Alzymologist/Kampela/docs/photos_C/IMG_20230130_222610.jpg

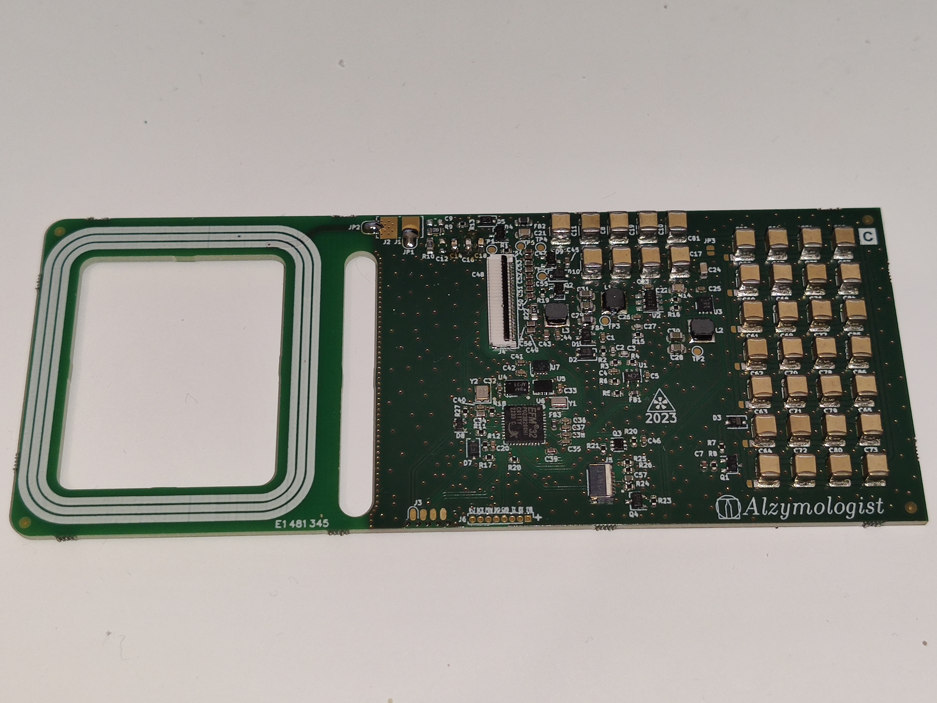
docs/photos_C/IMG_20230130_222610.jpg
