Alzymologist/Kampela/docs/photos_C/IMG_20230130_222933.jpg

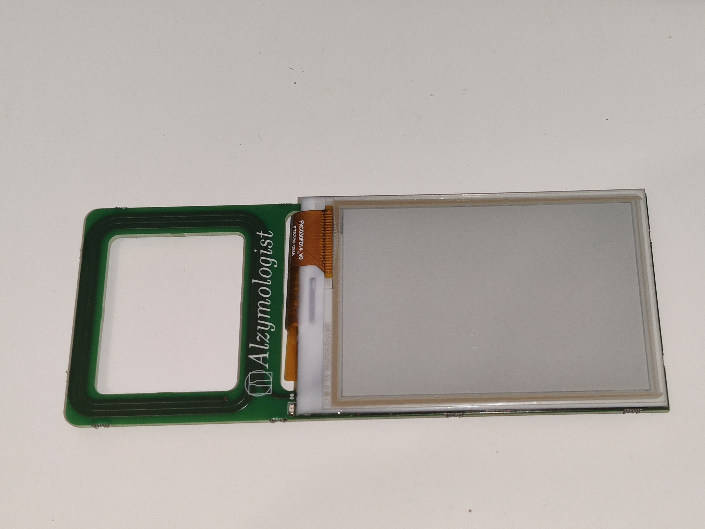
docs/photos_C/IMG_20230130_222933.jpg
