Alzymologist/Kampela/docs/photos_C/IMG_20230130_222946.jpg

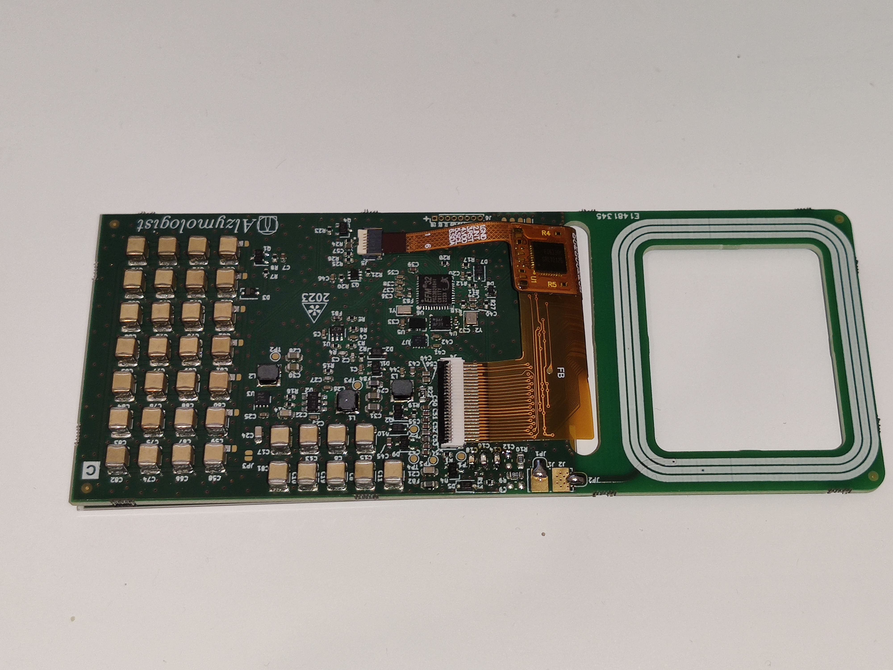
docs/photos_C/IMG_20230130_222946.jpg
