Alzymologist/Kampela/docs/photos_D/frame_1.jpg

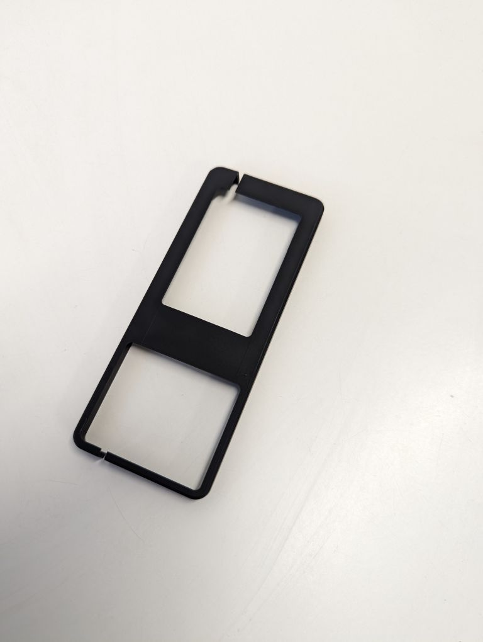
docs/photos_D/frame_1.jpg
