Alzymologist/Kampela/docs/photos_D/frame_2.jpg

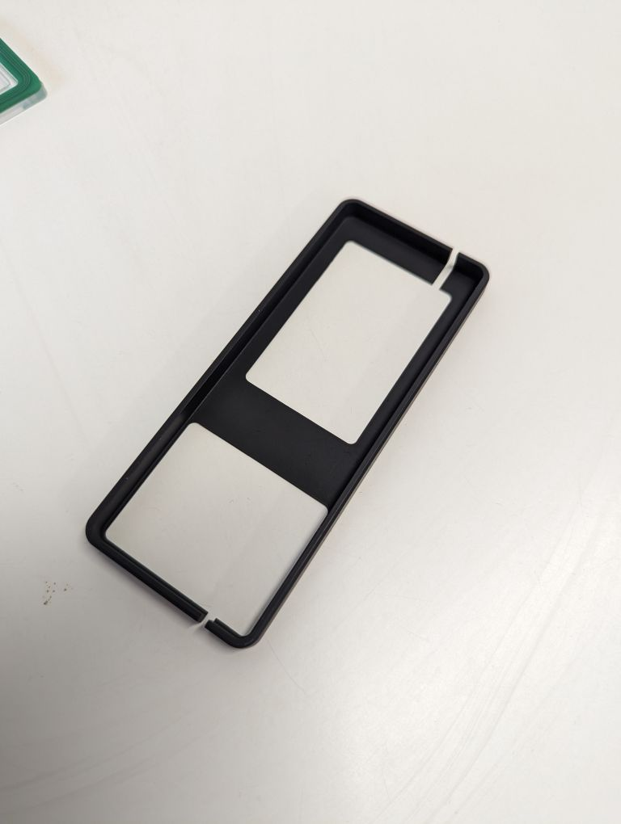
docs/photos_D/frame_2.jpg
