Alzymologist/Kampela/docs/photos_D/frame_3.jpg

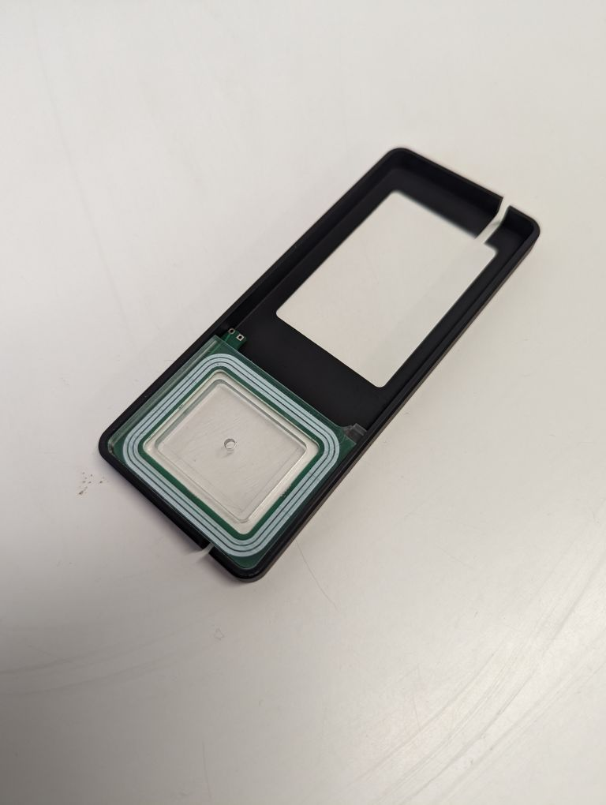
docs/photos_D/frame_3.jpg
