Alzymologist/Kampela/docs/photos_D/frame_4.jpg

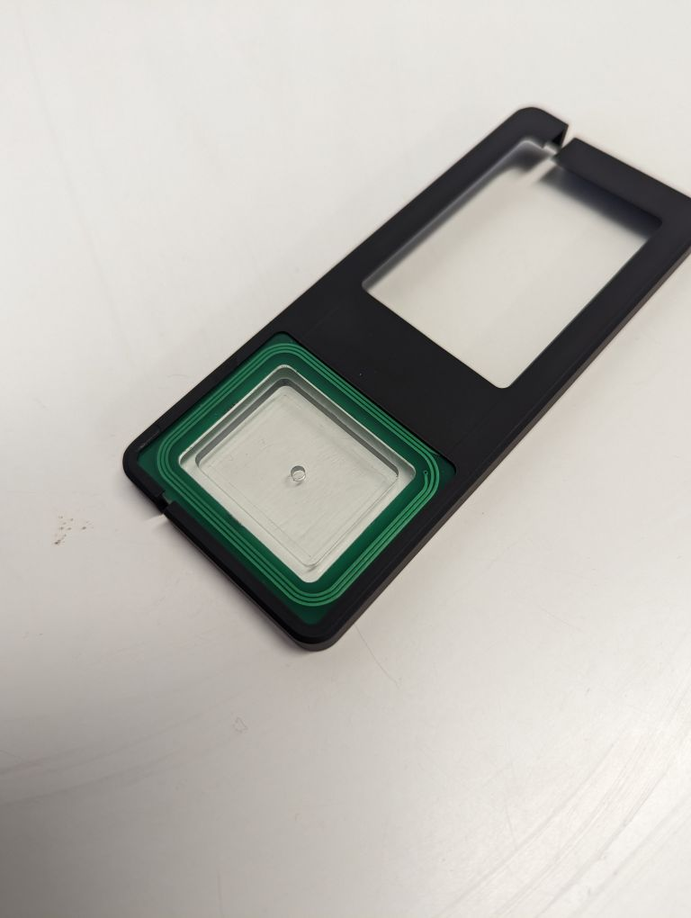
docs/photos_D/frame_4.jpg
