Alzymologist/Kampela/docs/photos_D/frame_5.jpg

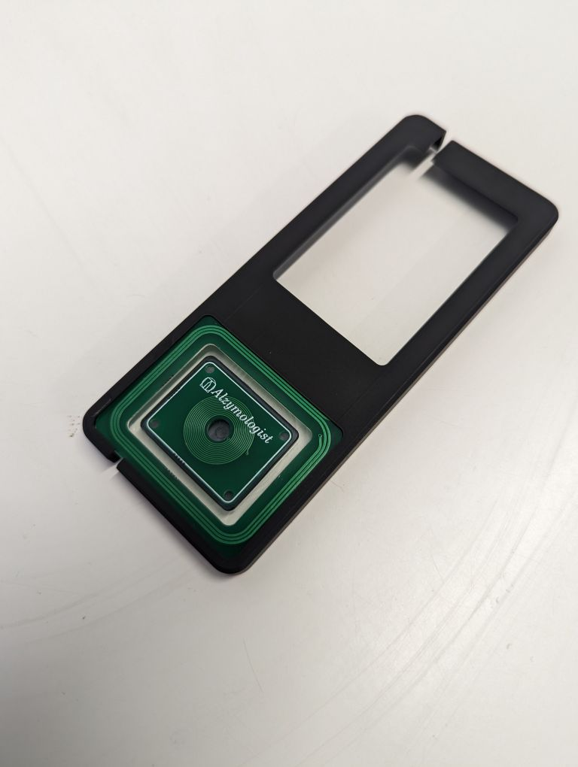
docs/photos_D/frame_5.jpg
