Alzymologist/Kampela/docs/photos_D/PCB_1.jpg

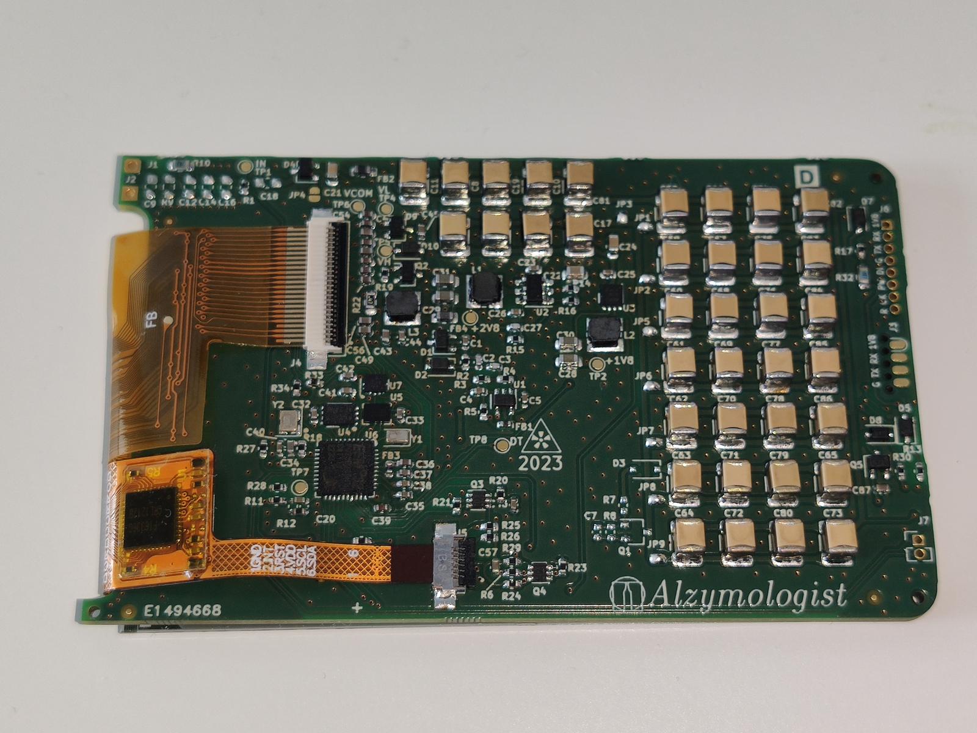
docs/photos_D/PCB_1.jpg
