Alzymologist/Kampela/docs/photos_D/PCB_2.jpg

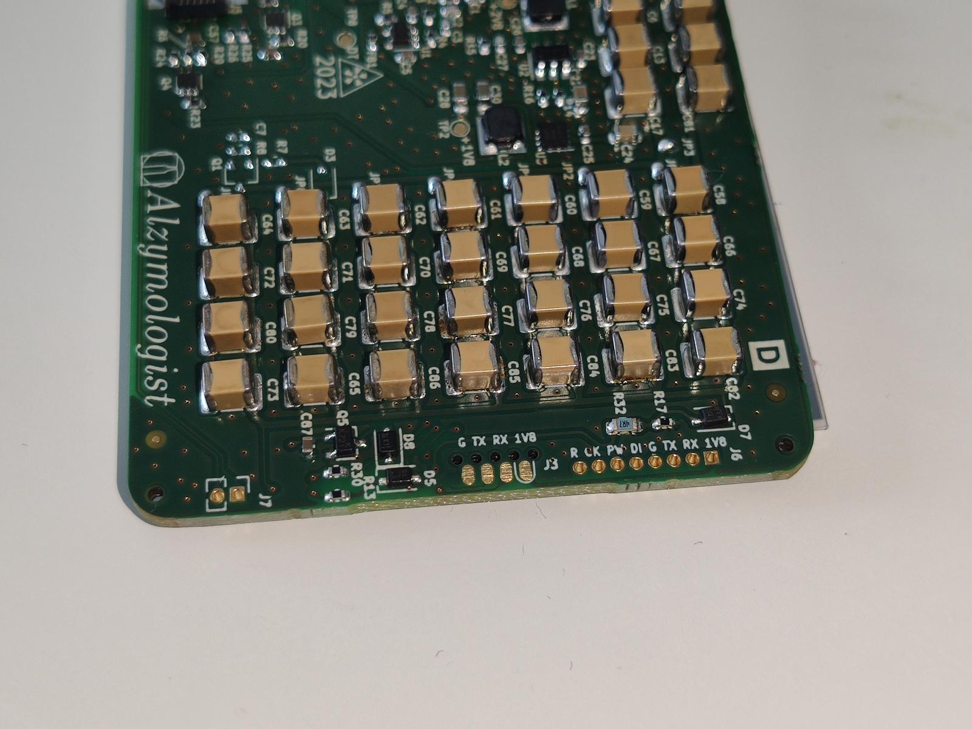
docs/photos_D/PCB_2.jpg
