Alzymologist/Kampela/docs/photos_D/PCB_3.jpg

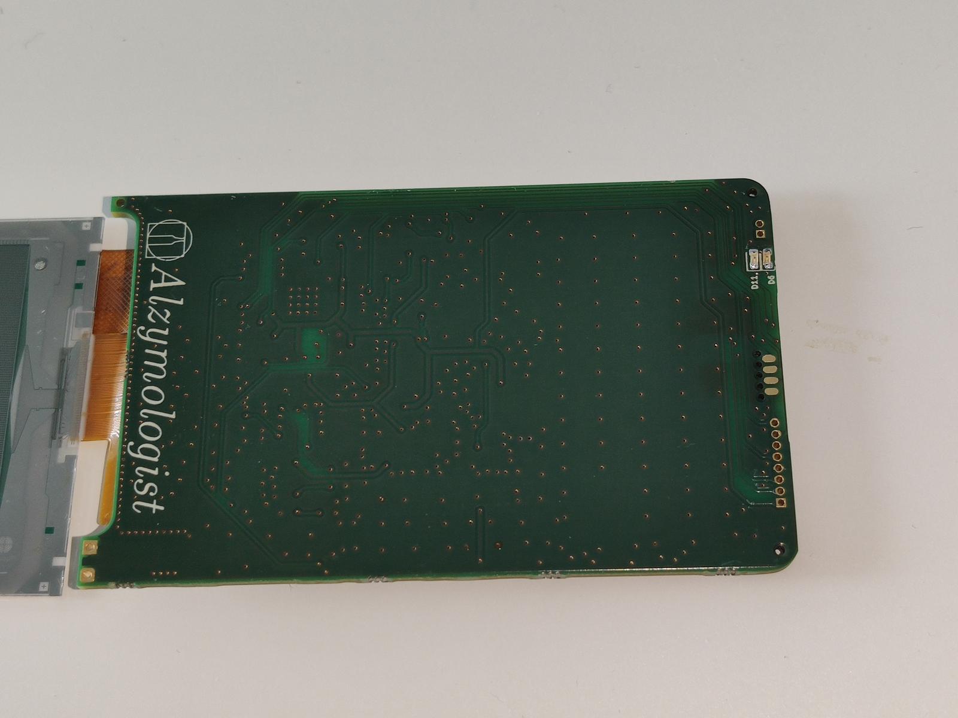
docs/photos_D/PCB_3.jpg
