Alzymologist/Kampela/docs/photos_D/tag.jpg

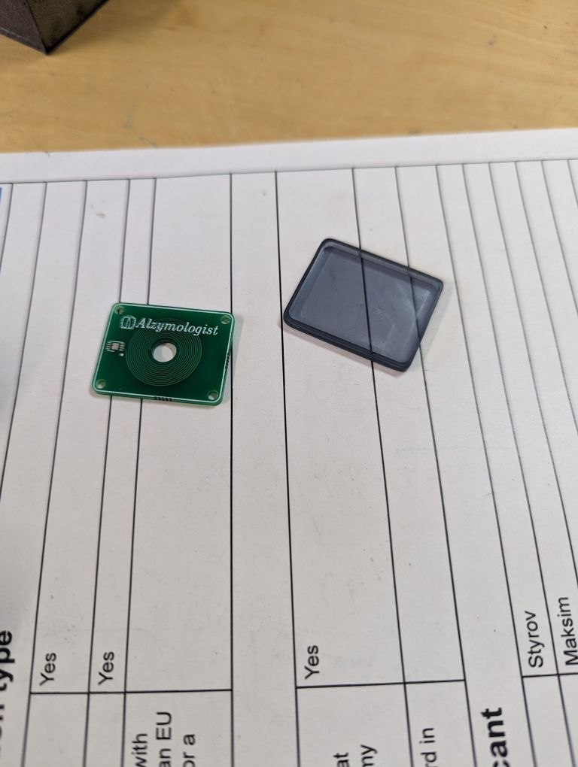
docs/photos_D/tag.jpg
