Alzymologist/Kampela/docs/renders/D_filled/bottom.png

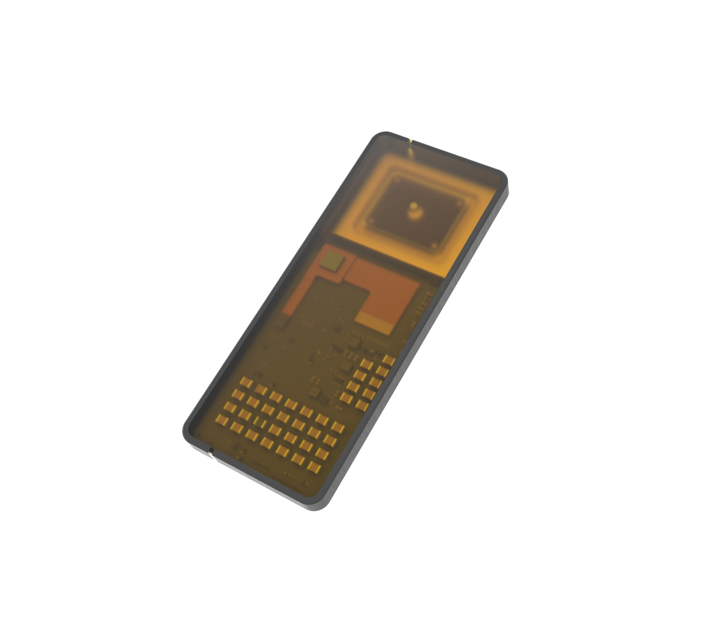
docs/renders/D_filled/bottom.png
