Alzymologist/Kampela/docs/renders/D_filled/top.png

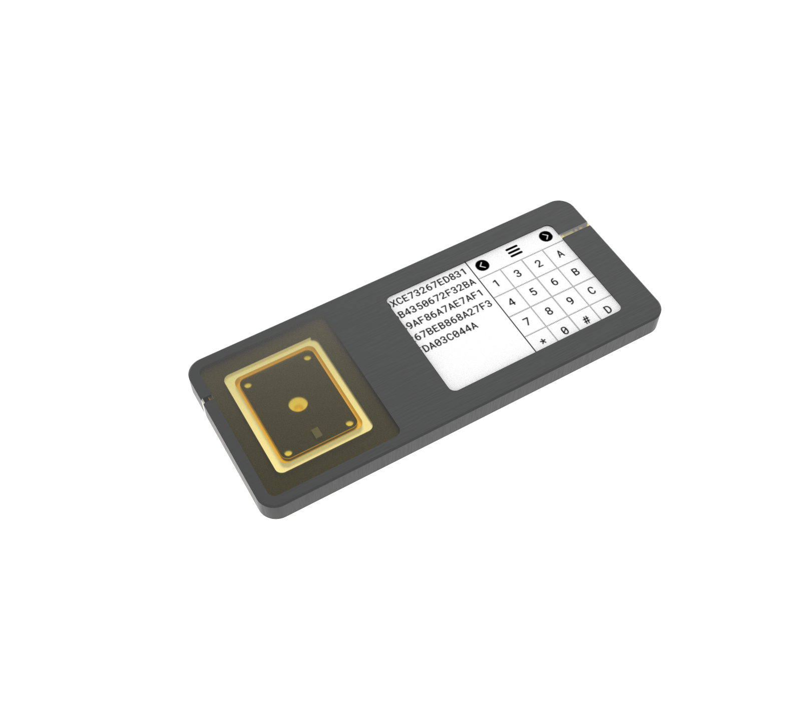
docs/renders/D_filled/top.png
