Alzymologist/Kampela/docs/screenshots/milestone 2/Derive.png

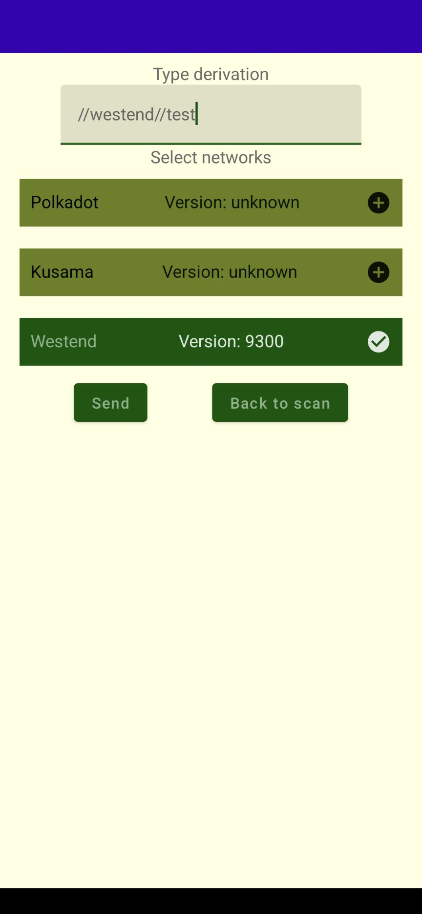
docs/screenshots/milestone 2/Derive.png
