Alzymologist/Kampela/docs/screenshots/milestone 2/Scan.png

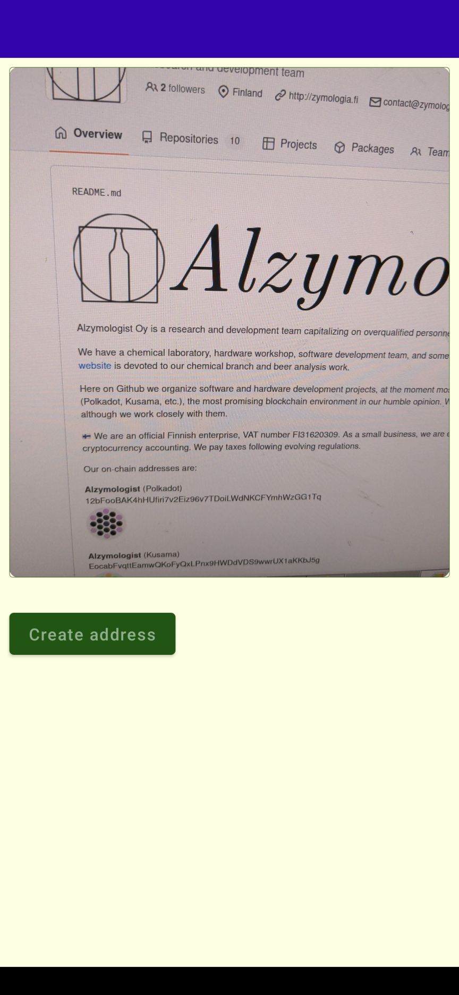
docs/screenshots/milestone 2/Scan.png
