Alzymologist/Kampela/docs/screenshots/milestone 2/TX.png

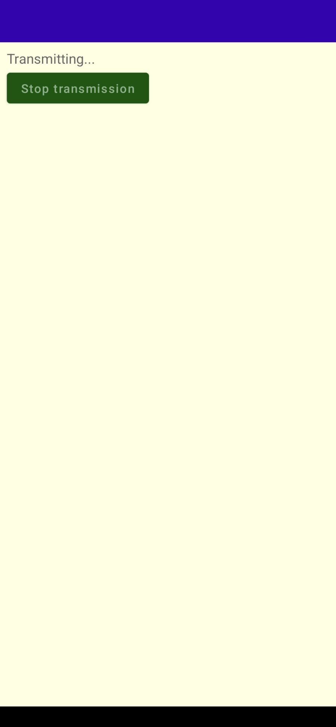
docs/screenshots/milestone 2/TX.png
