Alzymologist/Kampela/firmware/development/kampela/qr/AliceTransfer.png

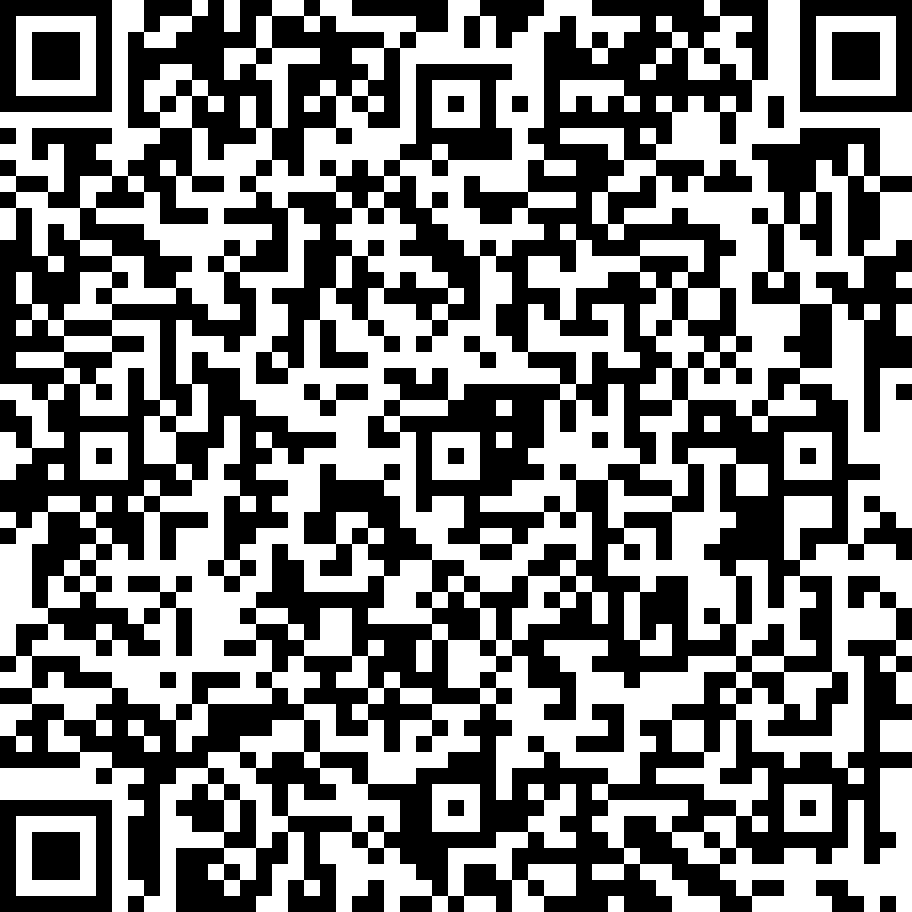
firmware/development/kampela/qr/AliceTransfer.png
