Alzymologist/Kampela/hardware/development/Kampela_C1_enclosure/renders/kampela_2.7_einc_touch.47.png

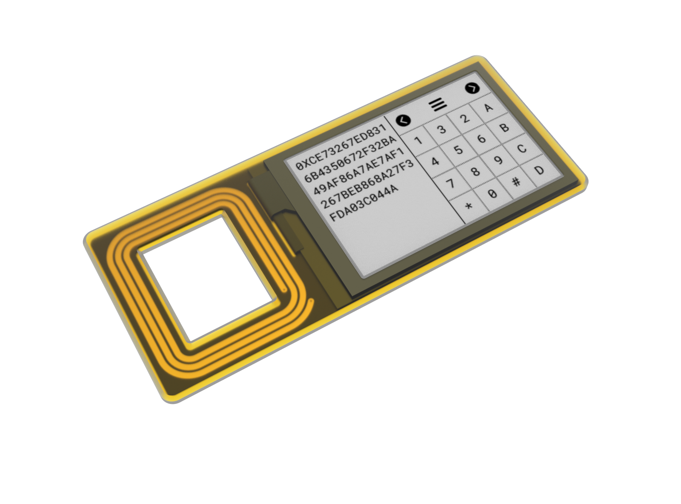
hardware/development/Kampela_C1_enclosure/renders/kampela_2.7_einc_touch.47.png
