Alzymologist/Kampela/firmware/development/C code/Camb_EFM_C1/user/Terminal12x16e.h

//
// Terminal12e.h
// Font library
// ----------------------------------


static const uint8_t Terminal12x16e[224][24] =
{
    0x00, 0x00, 0x00, 0x00, 0x00, 0x00, 0x00, 0x00, 0x00, 0x00, 0x00, 0x00, 0x00, 0x00, 0x00, 0x00, 0x00, 0x00, 0x00, 0x00, 0x00, 0x00, 0x00, 0x00,
    0x00, 0x00, 0x00, 0x00, 0x00, 0x00, 0x00, 0x00, 0x7C, 0x00, 0xFF, 0x33, 0xFF, 0x33, 0x7C, 0x00, 0x00, 0x00, 0x00, 0x00, 0x00, 0x00, 0x00, 0x00,
    0x00, 0x00, 0x00, 0x00, 0x00, 0x00, 0x3C, 0x00, 0x3C, 0x00, 0x00, 0x00, 0x00, 0x00, 0x3C, 0x00, 0x3C, 0x00, 0x00, 0x00, 0x00, 0x00, 0x00, 0x00,
    0x00, 0x00, 0x00, 0x02, 0x10, 0x1E, 0x90, 0x1F, 0xF0, 0x03, 0x7E, 0x02, 0x1E, 0x1E, 0x90, 0x1F, 0xF0, 0x03, 0x7E, 0x02, 0x1E, 0x00, 0x10, 0x00,
    0x00, 0x00, 0x00, 0x00, 0x78, 0x04, 0xFC, 0x0C, 0xCC, 0x0C, 0xFF, 0x3F, 0xFF, 0x3F, 0xCC, 0x0C, 0xCC, 0x0F, 0x88, 0x07, 0x00, 0x00, 0x00, 0x00,
    0x00, 0x00, 0x00, 0x30, 0x38, 0x38, 0x38, 0x1C, 0x38, 0x0E, 0x00, 0x07, 0x80, 0x03, 0xC0, 0x01, 0xE0, 0x38, 0x70, 0x38, 0x38, 0x38, 0x18, 0x00,
    0x00, 0x00, 0x00, 0x00, 0x00, 0x1F, 0xB8, 0x3F, 0xFC, 0x31, 0xC6, 0x21, 0xE2, 0x37, 0x3E, 0x1E, 0x1C, 0x1C, 0x00, 0x36, 0x00, 0x22, 0x00, 0x00,
    0x00, 0x00, 0x00, 0x00, 0x00, 0x00, 0x00, 0x00, 0x27, 0x00, 0x3F, 0x00, 0x1F, 0x00, 0x00, 0x00, 0x00, 0x00, 0x00, 0x00, 0x00, 0x00, 0x00, 0x00,
    0x00, 0x00, 0x00, 0x00, 0x00, 0x00, 0xF0, 0x03, 0xFC, 0x0F, 0xFE, 0x1F, 0x07, 0x38, 0x01, 0x20, 0x01, 0x20, 0x00, 0x00, 0x00, 0x00, 0x00, 0x00,
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
    0x00, 0x7E, 0x11, 0x11, 0x11, 0x7E,
    0x00, 0x7F, 0x49, 0x49, 0x49, 0x36,
    0x00, 0x3E, 0x41, 0x41, 0x41, 0x22,
    0x00, 0x7F, 0x41, 0x41, 0x41, 0x3E,
    0x00, 0x7F, 0x49, 0x49, 0x49, 0x41,
    0x00, 0x7F, 0x09, 0x09, 0x09, 0x01,
    0x00, 0x3E, 0x41, 0x49, 0x49, 0x7A,
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
};
