Alzymologist/Kampela/firmware/development/C code/Camb_EFM_C1/user/alzlogo.h

#pragma once


//200
static const uint8_t alzilogo[] =
{ 0xff, 0x83, 0x0f, 0xff, 0xff, 0xff, 0xff, 0xff, 0xff, 0xff, 0xff, 0xff, 0xff, 0xff, 0xff, 0xff, 0xff, 0xff, 0xff, 0xff, 0xff, 0xff, 0xff, 0xff, 0xff
, 0xfe, 0x3f, 0xe3, 0xff, 0xff, 0xff, 0xff, 0xff, 0xff, 0xff, 0xff, 0xff, 0xff, 0xff, 0xff, 0xff, 0xff, 0xff, 0xff, 0xff, 0xff, 0xff, 0xff, 0xff, 0xff
, 0xf8, 0xff, 0xf8, 0xff, 0xff, 0xf9, 0xff, 0xff, 0xff, 0xff, 0xff, 0xff, 0xff, 0xff, 0xff, 0xff, 0xff, 0xff, 0xff, 0xff, 0xff, 0xff, 0xff, 0xff, 0xff
, 0xf3, 0xff, 0xfe, 0x7f, 0xff, 0xf9, 0xff, 0x07, 0xff, 0xff, 0xff, 0xff, 0xff, 0xff, 0xff, 0xff, 0xfc, 0x1f, 0xff, 0xff, 0xff, 0xff, 0xff, 0xff, 0xff
, 0xc0, 0x00, 0x00, 0x1f, 0xff, 0xf1, 0xff, 0x87, 0xff, 0xff, 0xff, 0xff, 0xff, 0xff, 0xff, 0xff, 0xfe, 0x1f, 0xff, 0xff, 0xff, 0xfc, 0xff, 0xff, 0xff
, 0xcf, 0xfa, 0xff, 0x9f, 0xff, 0xf1, 0xff, 0xc7, 0xff, 0xff, 0xff, 0xff, 0xff, 0xff, 0xff, 0xff, 0xff, 0x3f, 0xff, 0xff, 0xff, 0xf8, 0xff, 0xff, 0xf3
, 0xdf, 0xf8, 0xff, 0xcf, 0xff, 0xe1, 0xff, 0xcf, 0xff, 0xff, 0xff, 0xff, 0xff, 0xff, 0xff, 0xff, 0xff, 0x3f, 0xff, 0xff, 0xff, 0xfd, 0xff, 0xff, 0xf3
, 0x9f, 0xfa, 0xff, 0xcf, 0xff, 0xc1, 0xff, 0xcf, 0xff, 0xff, 0xff, 0xff, 0xff, 0xff, 0xff, 0xff, 0xfe, 0x3f, 0xff, 0xff, 0xff, 0xff, 0xff, 0xff, 0xe3
, 0x9f, 0xfa, 0xff, 0xcf, 0xff, 0xd8, 0xff, 0x8f, 0xff, 0xff, 0xff, 0xff, 0xff, 0xff, 0xff, 0xff, 0xfe, 0x3f, 0xff, 0xff, 0xff, 0xff, 0xff, 0xff, 0xe3
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
, 0xc9, 0xf1, 0x9c, 0x1e, 0x01, 0xf1, 0x9e, 0x4f, 0xc4, 0x78, 0x3c, 0x78, 0xf0, 0x8f, 0x83, 0x30, 0xe0, 0x3e, 0x07, 0x3f, 0x79, 0xf9
, 0xe3, 0xf8, 0x3e, 0x3f, 0x23, 0xfc, 0x3f, 0x1f, 0xe0, 0xfc, 0x7e, 0x7c, 0xf8, 0x1f, 0xc7, 0xb1, 0xe0, 0x3e, 0x07, 0x1f, 0x79, 0xe1
, 0xff, 0xff, 0xff, 0xff, 0x3f, 0xff, 0xff, 0xff, 0xff, 0xff, 0xff, 0xff, 0xf9, 0xff, 0xff, 0xff, 0xff, 0xff, 0xff, 0x4f, 0x79, 0xc9
, 0xff, 0xff, 0xff, 0xff, 0x1f, 0xff, 0xff, 0xff, 0xff, 0xff, 0xff, 0xff, 0xf8, 0xe3, 0xff, 0xff, 0xff, 0xff, 0xff, 0x63, 0x79, 0x99
, 0xff, 0xff, 0xff, 0xff, 0x9e, 0x7f, 0xff, 0xff, 0xff, 0xff, 0xff, 0xff, 0xfc, 0xe3, 0xff, 0xff, 0xff, 0xff, 0xff, 0x78, 0x78, 0x39
, 0xff, 0xff, 0xff, 0xff, 0x8e, 0x7f, 0xff, 0xff, 0xff, 0xff, 0xff, 0xff, 0xfe, 0x33, 0xff, 0xff, 0xff, 0xff, 0xff, 0x00, 0x00, 0x03
, 0xff, 0xff, 0xff, 0xff, 0xe0, 0x7f, 0xff, 0xff, 0xff, 0xff, 0xff, 0xff, 0xff, 0x07, 0xff, 0xff, 0xff, 0xff, 0xff, 0xff, 0xff, 0xff

};
