Alzymologist/Kampela/firmware/development/C code/Camb_EFM_C1/user/EPD_Configuration.h

// SDK
#include "stdint.h"

#ifndef hV_CONFIGURATION_RELEASE
///
/// @brief Release
///
#define hV_CONFIGURATION_RELEASE
\
///
/// @name 1- List of supported Pervasive Displays screens
/// @see https://www.pervasivedisplays.com/products/
/// @{
///


/// @}

#endif // hV_CONFIGURATION_RELEASE
