Alzymologist/Kampela/firmware/development/kampela-ui/src/main.rs

//! This is simulator to develop Kampela UI mocks
#![cfg(feature="std")]
use embedded_graphics_core::{
    geometry::Size,
    pixelcolor::BinaryColor,
};
use embedded_graphics_simulator::{
    BinaryColorTheme, OutputSettingsBuilder, SimulatorDisplay, SimulatorEvent, Window,
};
use rand::{rngs::ThreadRng, thread_rng};
use std::{thread::sleep, time::Duration};
use clap::Parser;

#[macro_use]
extern crate lazy_static;

/// Amount of time required for full screen update; debounce
///  should be quite large as screen takes this much to clean
const SLOW_UPDATE_TIME: Duration = Duration::new(1, 0);

pub mod display_def;
pub use display_def::*;

mod platform;
use platform::Platform;

mod pin;
use pin::Pincode;

mod restore_or_generate;
mod seed_entry;

mod backup;

mod uistate;
use uistate::UIState;

mod data_state;
use data_state::{AppStateInit, NFCState, DataInit, StorageState};

mod transaction;
mod qr;

#[derive(Parser, Debug)]
#[command(author, version, about, long_about = None)]
struct Args {
    #[arg(short = 'I')]
    key_was_created: bool,

    #[arg(short = 'T')]
    transaction_received: bool,
}

impl DataInit<Args> for AppStateInit {
    fn new(params: Args) -> AppStateInit {
        let storage = StorageState {
            key_created: params.key_was_created,
        };

        let nfc = if params.transaction_received {
            NFCState::Transaction
        } else {
            NFCState::Empty
        };

        AppStateInit {
            nfc: nfc,
            storage: storage,
        }
    }
}

struct HALHandle {
    pub rng: ThreadRng,
}

impl HALHandle {
    pub fn new() -> Self {
        let rng = thread_rng();
        Self {
            rng: rng,
        }
    }
}

#[derive(Debug)]
struct DesktopSimulator {
    pin: Pincode,
    display: SimulatorDisplay<BinaryColor>,
    seed: Vec<u8>,
    transaction: String,
    extensions: String,
    signature: Option<[u8; 130]>,
}

impl DesktopSimulator {
    pub fn new(init_state: &AppStateInit, h: &mut HALHandle) -> Self {
        let pin = Pincode::new(&mut h.rng, false);
        let display = SimulatorDisplay::new(Size::new(SCREEN_SIZE_X, SCREEN_SIZE_Y));
        let transaction = match init_state.nfc {
            NFCState::Empty => String::new(),
            NFCState::Transaction => String::from("Hello, this is a transaction!"),
        };
        let extensions = match init_state.nfc {
            NFCState::Empty => String::new(),
            NFCState::Transaction => String::from("Hello, this is a transaction!"),
        };
        let signature = match init_state.nfc {
            NFCState::Empty => None,
            NFCState::Transaction => Some([0u8; 130]),
        };
        Self {
            pin: pin,
            display: display,
            seed: Vec::new(),
            transaction: transaction,
            extensions: extensions,
            signature: signature,
        }
    }
}

impl Platform for DesktopSimulator {
    type HAL = HALHandle;
    type Rng<'a> = &'a mut ThreadRng;
    type Display = SimulatorDisplay<BinaryColor>;

    fn rng<'a>(h: &'a mut Self::HAL) -> Self::Rng<'a> {
        &mut h.rng
    }

    fn pin(&self) -> &Pincode {
        &self.pin
    }

    fn pin_mut(&mut self) -> &mut Pincode {
        &mut self.pin
    }

    fn display(&mut self) -> &mut Self::Display {
        &mut self.display
    }

    fn pin_display(&mut self) -> (&mut Pincode, &mut Self::Display) {
        (&mut self.pin, &mut self.display)
    }

    fn set_entropy(&mut self, e: &[u8]) {
        self.seed = e.to_vec();
    }

    fn entropy_display(&mut self) -> (&Vec<u8>, &mut Self::Display) {
        (&self.seed, &mut self.display)
    }

    fn set_transaction(&mut self, transaction: String, extensions: String, signature: [u8; 130]) {
        self.transaction = transaction;
        self.extensions = extensions;
        self.signature = Some(signature);
    }

    fn transaction(&mut self) -> Option<(&str, &mut Self::Display)> {
        if self.transaction != "" {
            Some((&self.transaction, &mut self.display))
        } else {
            None
        }
    }

    fn extensions(&mut self) -> Option<(&str, &mut Self::Display)> {
        if self.extensions != "" {
            Some((&self.extensions, &mut self.display))
        } else {
            None
        }
    }

    fn signature(&mut self) -> (&[u8; 130], &mut Self::Display) {
        if let Some(ref a) = self.signature {
            (a, &mut self.display)
        } else {
            panic!("qr not ready!");
        }
    }
}


fn main() {
    let args = Args::parse();
    let init_data_state = AppStateInit::new(args);
    println!("{:?}", init_data_state);

    /*
    // Prepare
    let mut display: SimulatorDisplay<BinaryColor> =
        SimulatorDisplay::new(Size::new(SCREEN_SIZE_X, SCREEN_SIZE_Y));
*/

    let mut h = HALHandle::new();
    let desktop = DesktopSimulator::new(&init_data_state, &mut h);

    let mut state = UIState::new(desktop);

    // Draw
    let output_settings = OutputSettingsBuilder::new()
        .theme(BinaryColorTheme::Inverted)
        .build();
    let mut window = Window::new("Hello world", &output_settings); //.show_static(&display);
    
    let mut update = uistate::UpdateRequest::new();
    update.set_slow();

    // event loop:
    //
    // 1. draw
    // 2. collect input
    // 3. handle input
    // 4. do internal things
    loop {
        // display event; it would be delayed
        if update.read_fast() {
            window.update(state.display());
            println!("skip {} events in fast update", window.events().count());
            //no-op for non-EPD
        }
        if update.read_slow() {
            match state.render::<SimulatorDisplay<BinaryColor>>() {
                    Ok(()) => (),
                    Err(e) => println!("{:?}", e),
                };
            sleep(SLOW_UPDATE_TIME);
            window.update(state.display());
            println!("skip {} events in slow update", window.events().count());
        }

        // this collects ui events, do not remove or simulator will crash
        window.update(state.display());

        // handle input (only pushes are valid in Kampela)
        for event in window.events() {
            match event {
                SimulatorEvent::MouseButtonDown {
                    mouse_btn: _,
                    point,
                } => {
                    println!("{}", point);
                        match state.handle_event::<SimulatorDisplay<BinaryColor>>(point, &mut h) {
                            Ok(a) => update = a,
                            Err(e) => println!("{e}"),
                        };
                }
                SimulatorEvent::Quit => return,
                _ => (),
            }
        }

        //and here is some loop time for other things
    }
}
