Alzymologist/Kampela/firmware/development/C code/Camb_EFM_C1/user/Ap_29demo.h

//////////////////////Bureau brush refreshes the number/////////////////////
//Digital presentation array
const unsigned char gImage_num1[128] = { /* 0X02,0X01,0X20,0X00,0X20,0X00, */
0xFF,0xFF,0xFF,0xFF,0xFF,0xFF,0xFF,0xFF,0xFF,0xFF,0xFF,0xFF,0xFF,0xFF,0xFF,0xFF,
0xFF,0xFF,0xFF,0xFF,0xFF,0xFF,0xFF,0xFF,0xFF,0xFF,0xFF,0xFF,0xFF,0xFF,0xFF,0xFF,
0xFF,0xFF,0xFF,0xFF,0xFF,0xFF,0xFF,0xFF,0xFF,0xFF,0xFF,0xFF,0xFF,0xDF,0xFF,0xF7,
0xFF,0xDF,0xFF,0xF7,0xFF,0xDF,0xFF,0xF7,0xFF,0xDF,0xFF,0xE7,0xFF,0x80,0x00,0x07,
0xFF,0x00,0x00,0x07,0xFF,0x00,0x00,0x07,0xFF,0xFF,0xFF,0xE7,0xFF,0xFF,0xFF,0xF7,
0xFF,0xFF,0xFF,0xF7,0xFF,0xFF,0xFF,0xF7,0xFF,0xFF,0xFF,0xFF,0xFF,0xFF,0xFF,0xFF,
0xFF,0xFF,0xFF,0xFF,0xFF,0xFF,0xFF,0xFF,0xFF,0xFF,0xFF,0xFF,0xFF,0xFF,0xFF,0xFF,
0xFF,0xFF,0xFF,0xFF,0xFF,0xFF,0xFF,0xFF,0xFF,0xFF,0xFF,0xFF,0xFF,0xFF,0xFF,0xFF,
};

const unsigned char gImage_num2[128] = { /* 0X02,0X01,0X20,0X00,0X20,0X00, */
0xFF,0xFF,0xFF,0xFF,0xFF,0xFF,0xFF,0xFF,0xFF,0xFF,0xFF,0xFF,0xFF,0xFF,0xFF,0xFF,
0xFF,0xFF,0xFF,0xFF,0xFF,0xFF,0xFF,0xFF,0xFF,0xFF,0xFF,0xFF,0xFF,0xFF,0xFF,0xFF,
0xFF,0xFF,0xFF,0xFF,0xFF,0xFF,0xFF,0xFF,0xFF,0xE1,0xFF,0xC7,0xFF,0xC1,0xFF,0x87,
0xFF,0x99,0xFF,0x27,0xFF,0x3F,0xFE,0x67,0xFF,0x7F,0xFC,0xE7,0xFF,0x7F,0xF9,0xE7,
0xFF,0x7F,0xF3,0xE7,0xFF,0x7F,0xE7,0xE7,0xFF,0x3F,0xCF,0xE7,0xFF,0x1F,0x1F,0xE7,
0xFF,0x80,0x3F,0xC7,0xFF,0x80,0x7E,0x07,0xFF,0xE0,0xFE,0x1F,0xFF,0xFF,0xFF,0xFF,
0xFF,0xFF,0xFF,0xFF,0xFF,0xFF,0xFF,0xFF,0xFF,0xFF,0xFF,0xFF,0xFF,0xFF,0xFF,0xFF,
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
0XFF,0XFF,0XFF,0XFF,0XFF,0XFF,0XFF,0XFF,0XFF,0XFF,0XFF,0XFF,0XFF,0XFF,0XFF,0XFF,
0XFF,0XFF,0XFF,0XFF,0XFF,0XFF,0XFF,0XFF,0XFF,0XFF,0XFF,0XFF,0XFF,0XFF,0XFF,0XFF,
0XFF,0XFF,0XFF,0XFF,0XFF,0XFF,0XFF,0XFF,0XFF,0XFF,0XFF,0XFF,0XFF,0XFF,0XFF,0XFF,
0XFF,0XFF,0XFF,0XFF,0XFF,0XFF,0XFF,0XFF,};
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
